radhoo/geiger-dosimeter-v3-4/121.png

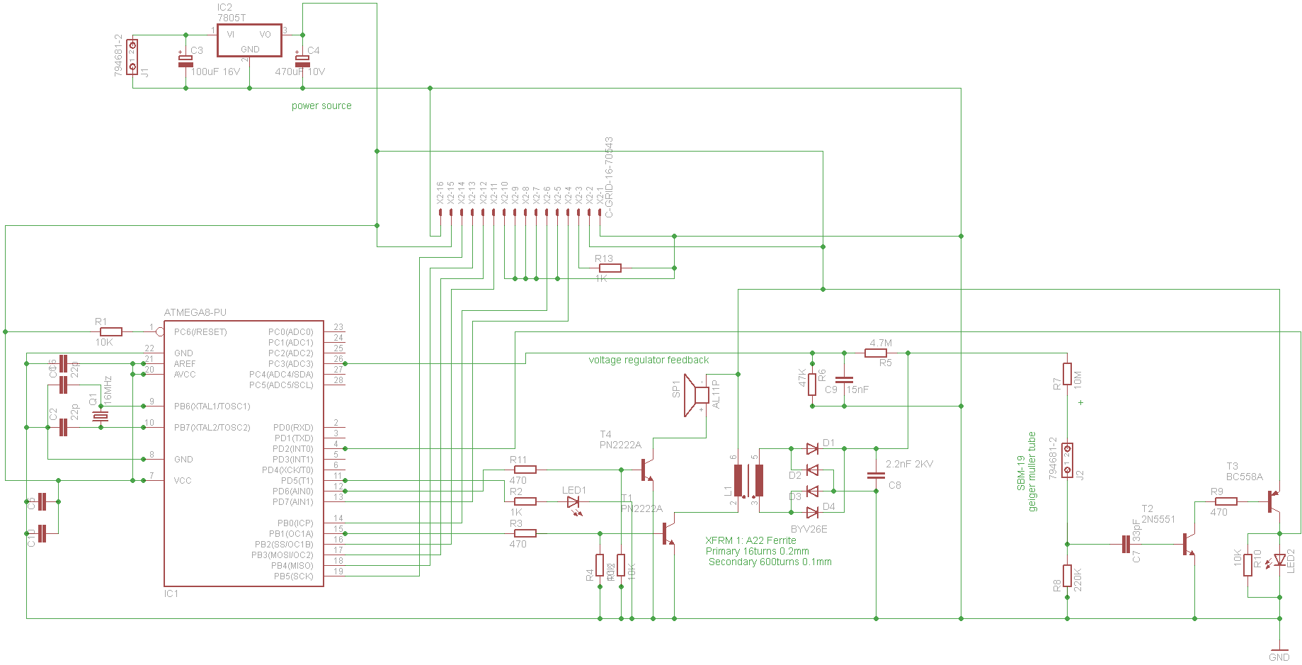
121.png
